hernss/pressure_sensor_interface/PlacaBase/modelos3D/PJ-002A.step

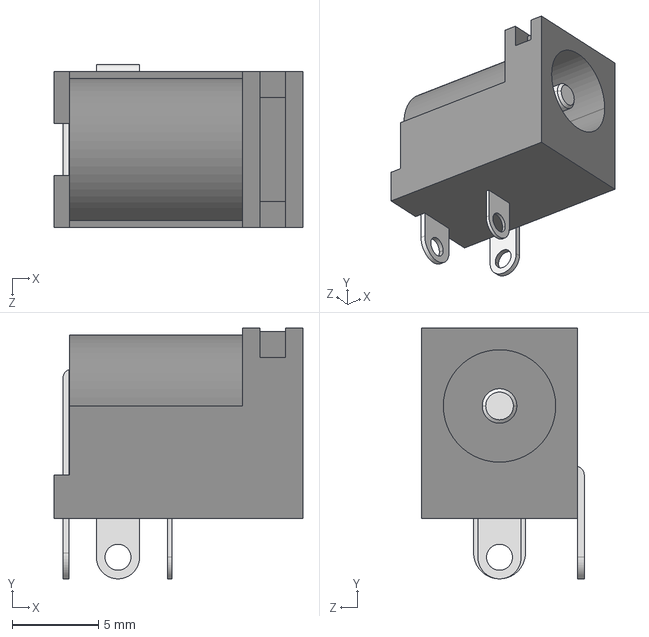
[picture p46: CAD file, 2023-02-13]
PlacaBase/modelos3D/PJ-002A.step
14.4 x 14.5 x 9.40 mm
