hernss/pressure_sensor_interface/Panelizado/modelos3D/Omron-G5LE-14.step

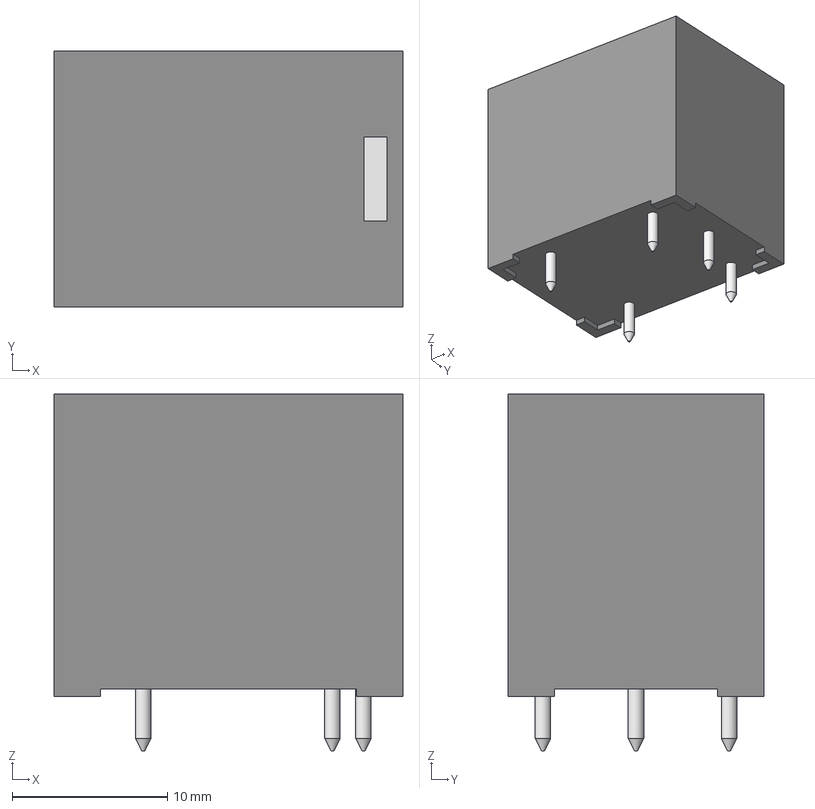
[picture p47: CAD file, 2023-02-13]
Panelizado/modelos3D/Omron-G5LE-14.step
22.5 x 16.5 x 23.0 mm
