hernss/pressure_sensor_interface/Panelizado/modelos3D/ABS25.STEP

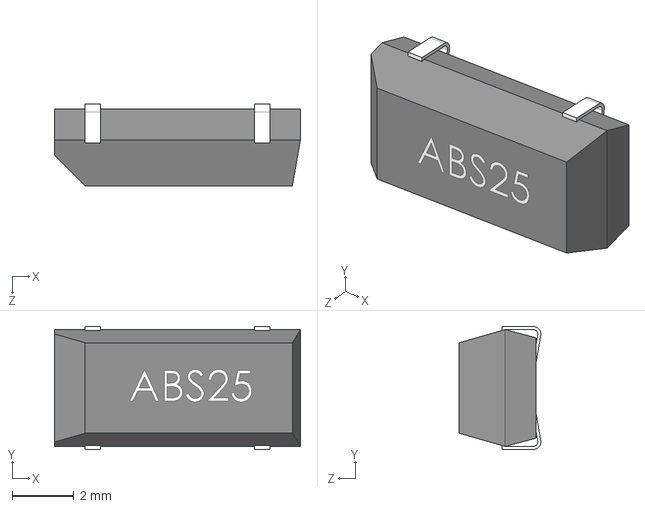
[picture p48: CAD file, 2023-02-13]
Panelizado/modelos3D/ABS25.STEP
8.00 x 4.00 x 2.66 mm
